pneumaticdeath/DK63-calisto-partsAnB/DK63_plug-2.stl

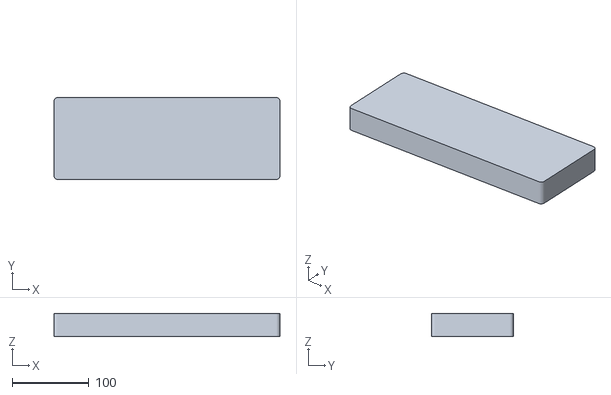
[picture p18: CAD file, 2025-03-30]
DK63_plug-2.stl
293.7 x 106.4 x 30.2
