pneumaticdeath/DK63-calisto-partsAnB/DK63_plug.stl

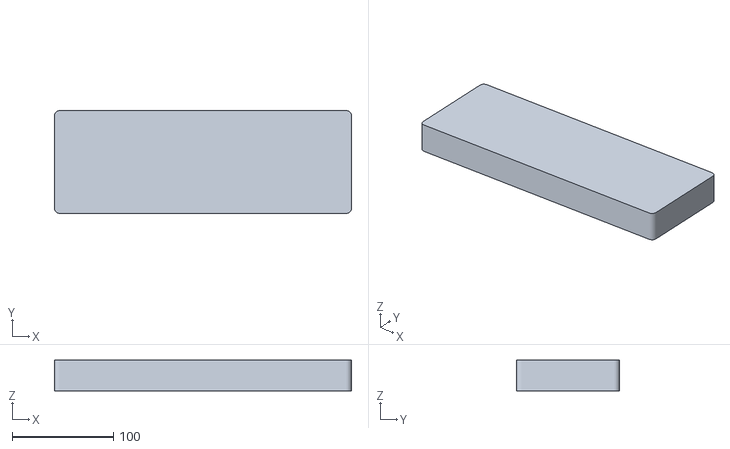
[picture p19: CAD file, 2025-03-30]
DK63_plug.stl
293.7 x 101.6 x 30.2
